EmenstaNougat/ESP32-BlueJammer/Gallery/Back-ESP32-BlueJammerDIY-PCB.png

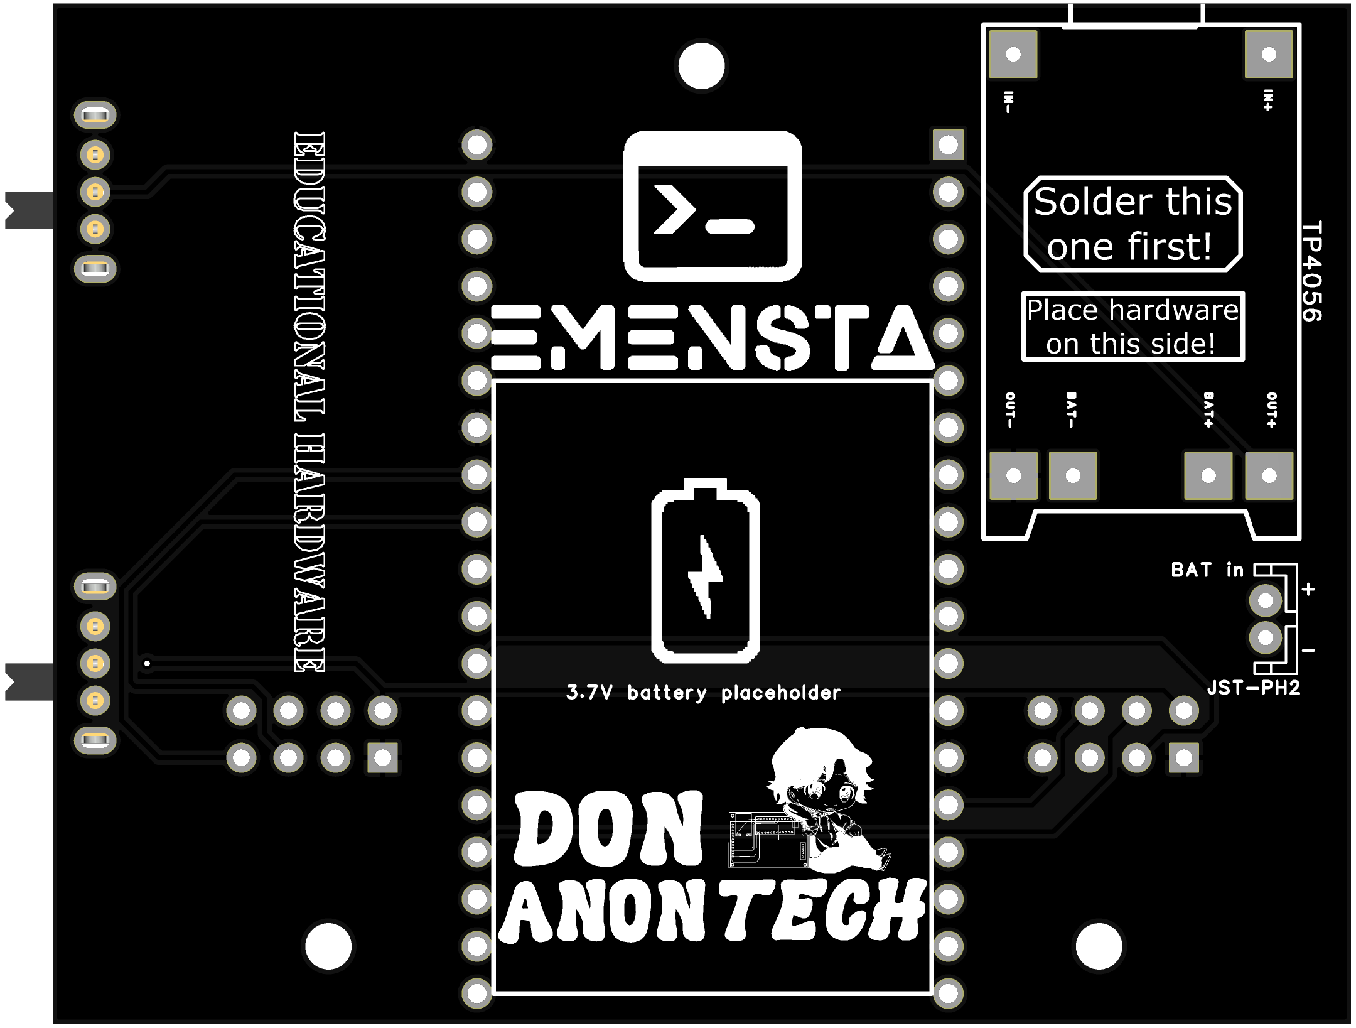
Gallery/Back-ESP32-BlueJammerDIY-PCB.png
