EmenstaNougat/ESP32-BlueJammer/Gallery/ESP32-BlueJammer-DIY-PCB.jpg

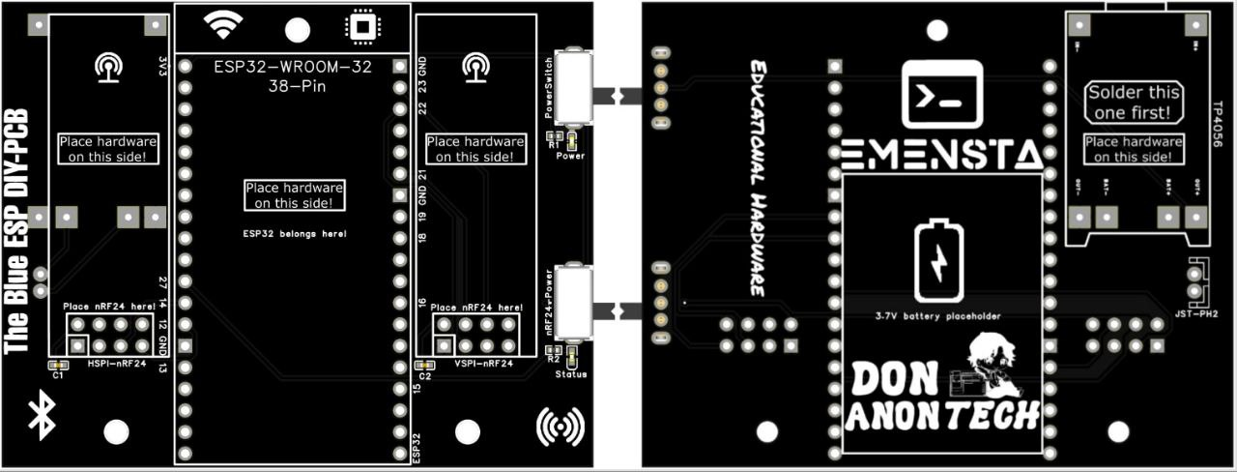
Gallery/ESP32-BlueJammer-DIY-PCB.jpg
