EmenstaNougat/ESP32-BlueJammer/Gallery/ESP32-BlueJammerBy@emensta.jpg

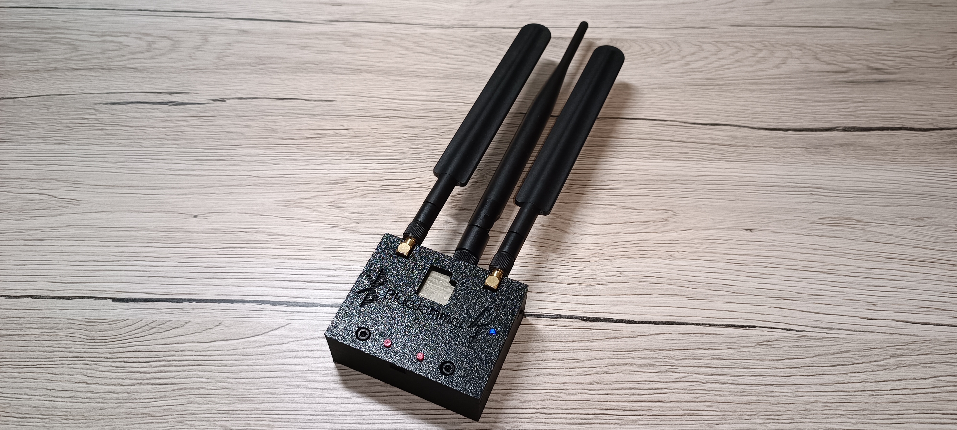
Gallery/ESP32-BlueJammerBy@emensta.jpg
