EmenstaNougat/ESP32-BlueJammer/Gallery/ESP32-BlueJammerUSB_C_chargerWithIndicators.jpg

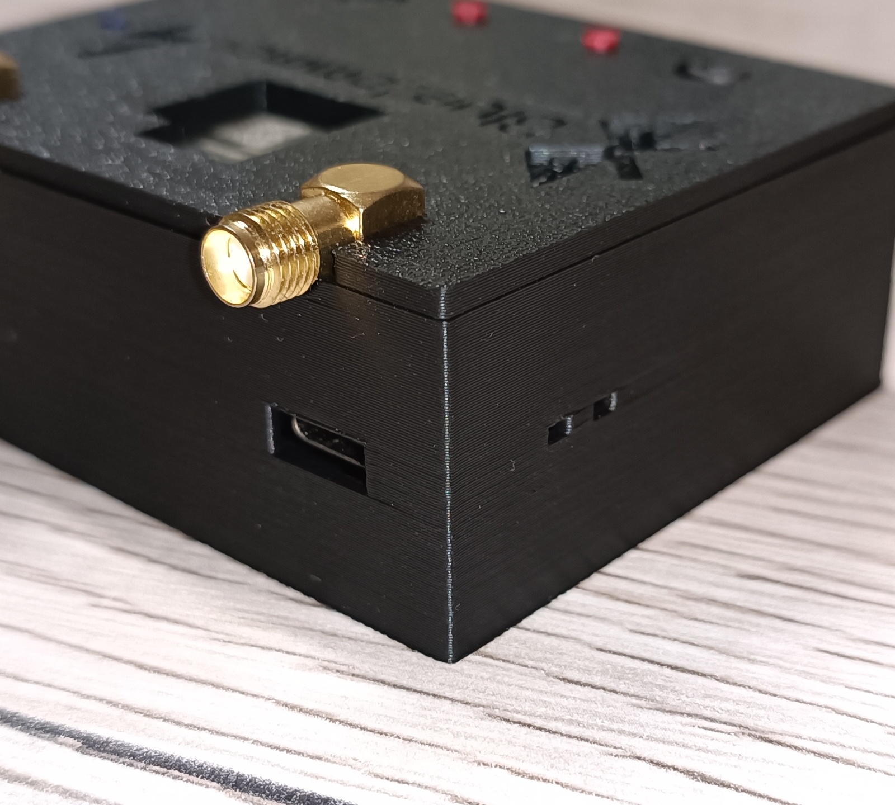
Gallery/ESP32-BlueJammerUSB_C_chargerWithIndicators.jpg
