EmenstaNougat/ESP32-BlueJammer/Gallery/ESP32BlueJammerFlasher.png

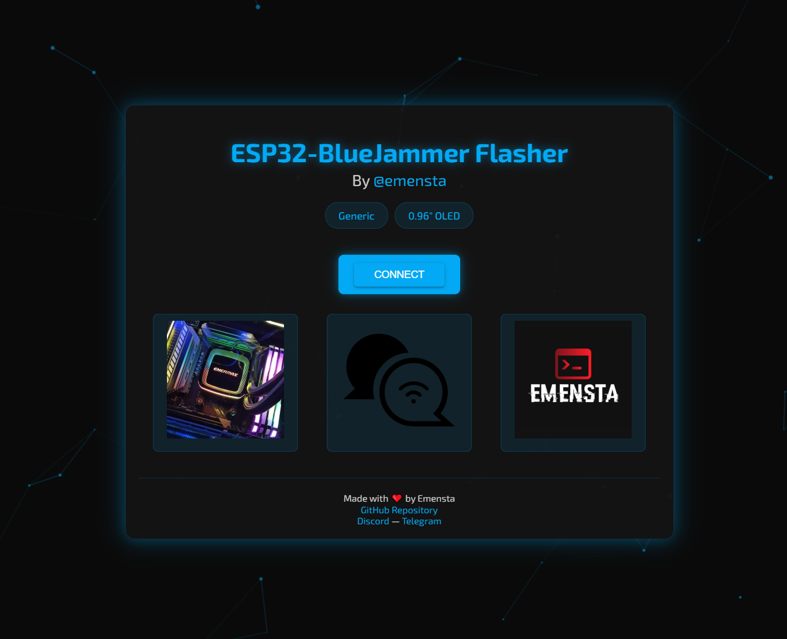
Gallery/ESP32BlueJammerFlasher.png
