EmenstaNougat/ESP32-BlueJammer/Gallery/Front-ESP32-BlueJammerDIY-PCB.png

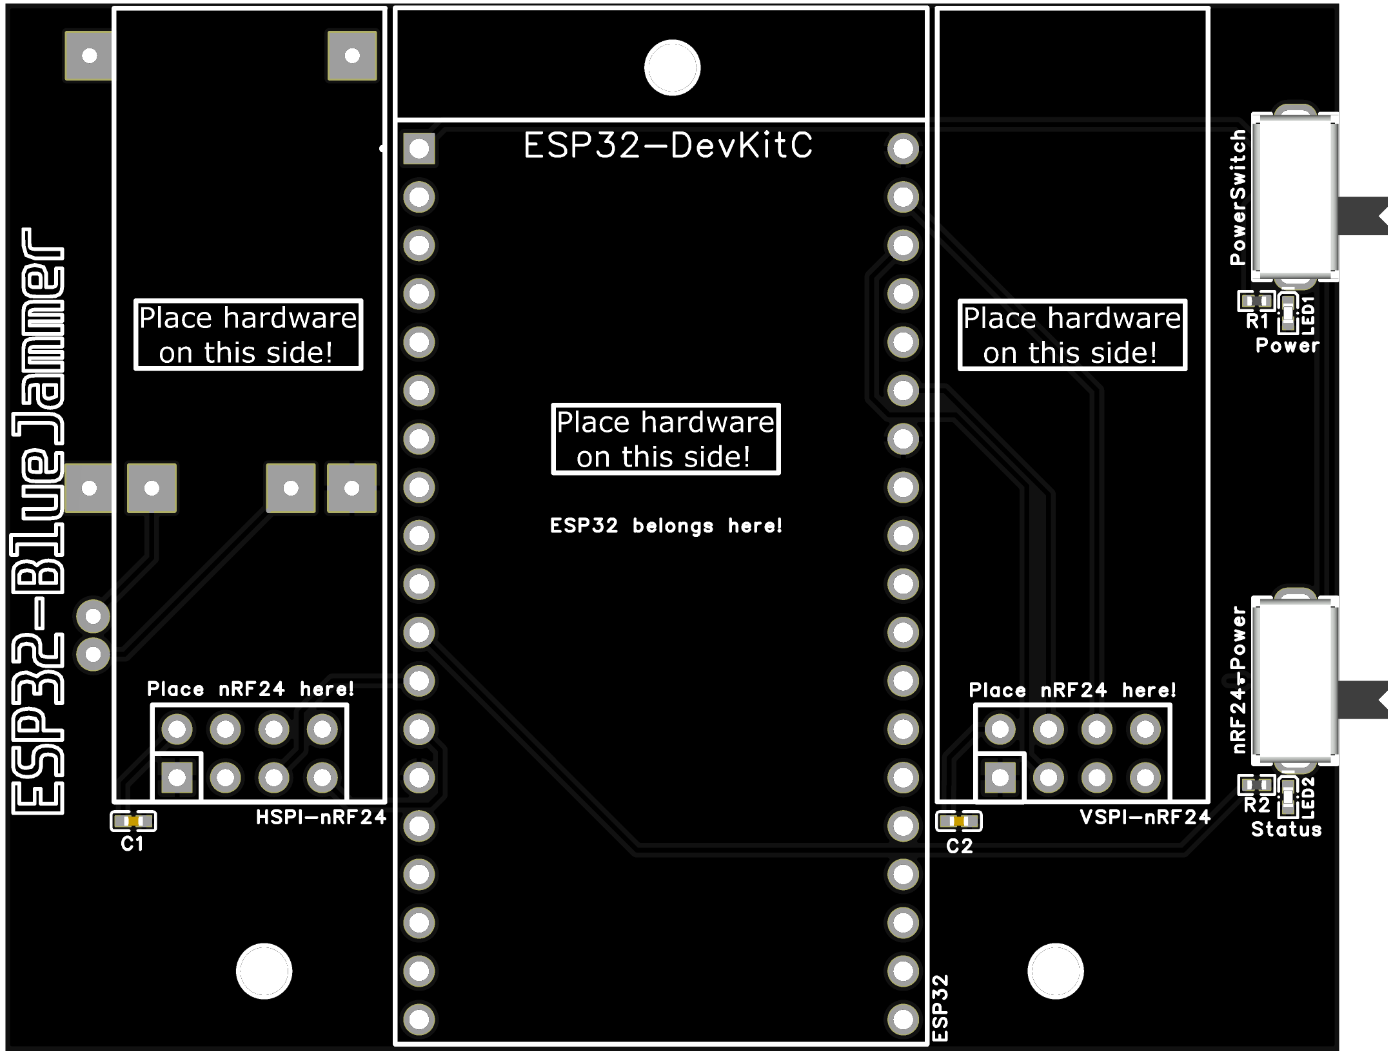
Gallery/Front-ESP32-BlueJammerDIY-PCB.png
