EmenstaNougat/ESP32-BlueJammer/Gallery/TheBlueESP.png

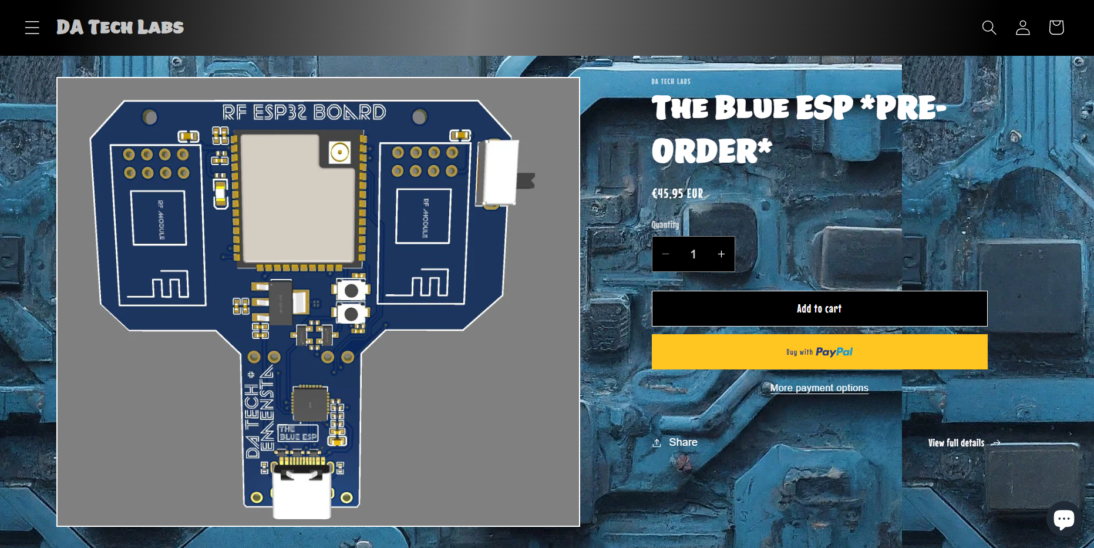
Gallery/TheBlueESP.png
