EmenstaNougat/ESP32-BlueJammer/Gallery/V4-ESP32-BlueJammer3DCaseView.png

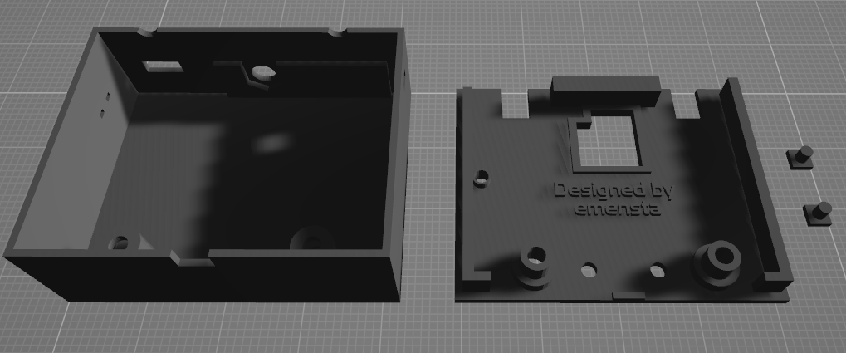
Gallery/V4-ESP32-BlueJammer3DCaseView.png
